YannickKoenig/DIY-Laboratory-Power-Supply/software/displaylib_LED_PICO/include/displaylib_LED_PICO/common_data.hpp

/*!
	@file   common_data.hpp
	@brief  common data class for LED segment modules.
*/

#ifndef DATALIB_COMMON_H
#define DATALIB_COMMON_H

#include <cstdint>
#include <string>

/*!
	@class CommonData
	@brief Class that provides access to common data
 */
class CommonData
{
public:
	/*! Alignment of text on display */
	enum TextAlignment_e : uint8_t
	{
		AlignLeft = 0,		/**< Align text to the left on display */
		AlignRight = 1,		/**< Align text to the right on display */
		AlignRightZeros = 2 /**< Add leading zeros to the right aligned text */
	};
	/*! Activate Decimal point segment */
	enum DecimalPoint_e : uint8_t
	{
		DecPointOff = 0, /**< Decimal point segment off */
		DecPointOn = 1	 /**< Decimal point segment on */
	};

	static constexpr const char *displaylib_LED_VersionNum = "2.1.0";
	bool displaylib_LED_debug = false; /**< debug flag, true = debug mode on, extra infomation written to console */

protected:
	// Font offsets
	static constexpr uint8_t _ASCII_FONT_OFFSET = 0x20;		/**< Offset in the ASCII table for font Start position */
	static constexpr uint8_t _ASCII_FONT_END = 0x7B;		/**< End of ASCII Table + 1*/
	static constexpr uint8_t _ASCII_FONT_HEX_OFFSET = 0x10; /**< ASCII table offset to reach the number position */
	// Decimal point masks
	static constexpr uint8_t DEC_POINT_7_MASK = 0x80;	  /**< Mask to switch on 7 seg decimal point */
	static constexpr uint16_t DEC_POINT_9_MASK = 0x0200;  /**< Mask to switch on 9 seg decimal point */
	static constexpr uint16_t DEC_POINT_14_MASK = 0x4000; /**< Mask to switch on 14 seg decimal point */
};

#endif
